XinyiC222/KeyboardX81/Project Files/Kicad/Amelia's Keyboard.kicad_sch

## KiCad design Project Files/Kicad/Amelia's Keyboard.kicad_sch (2026-07-13)

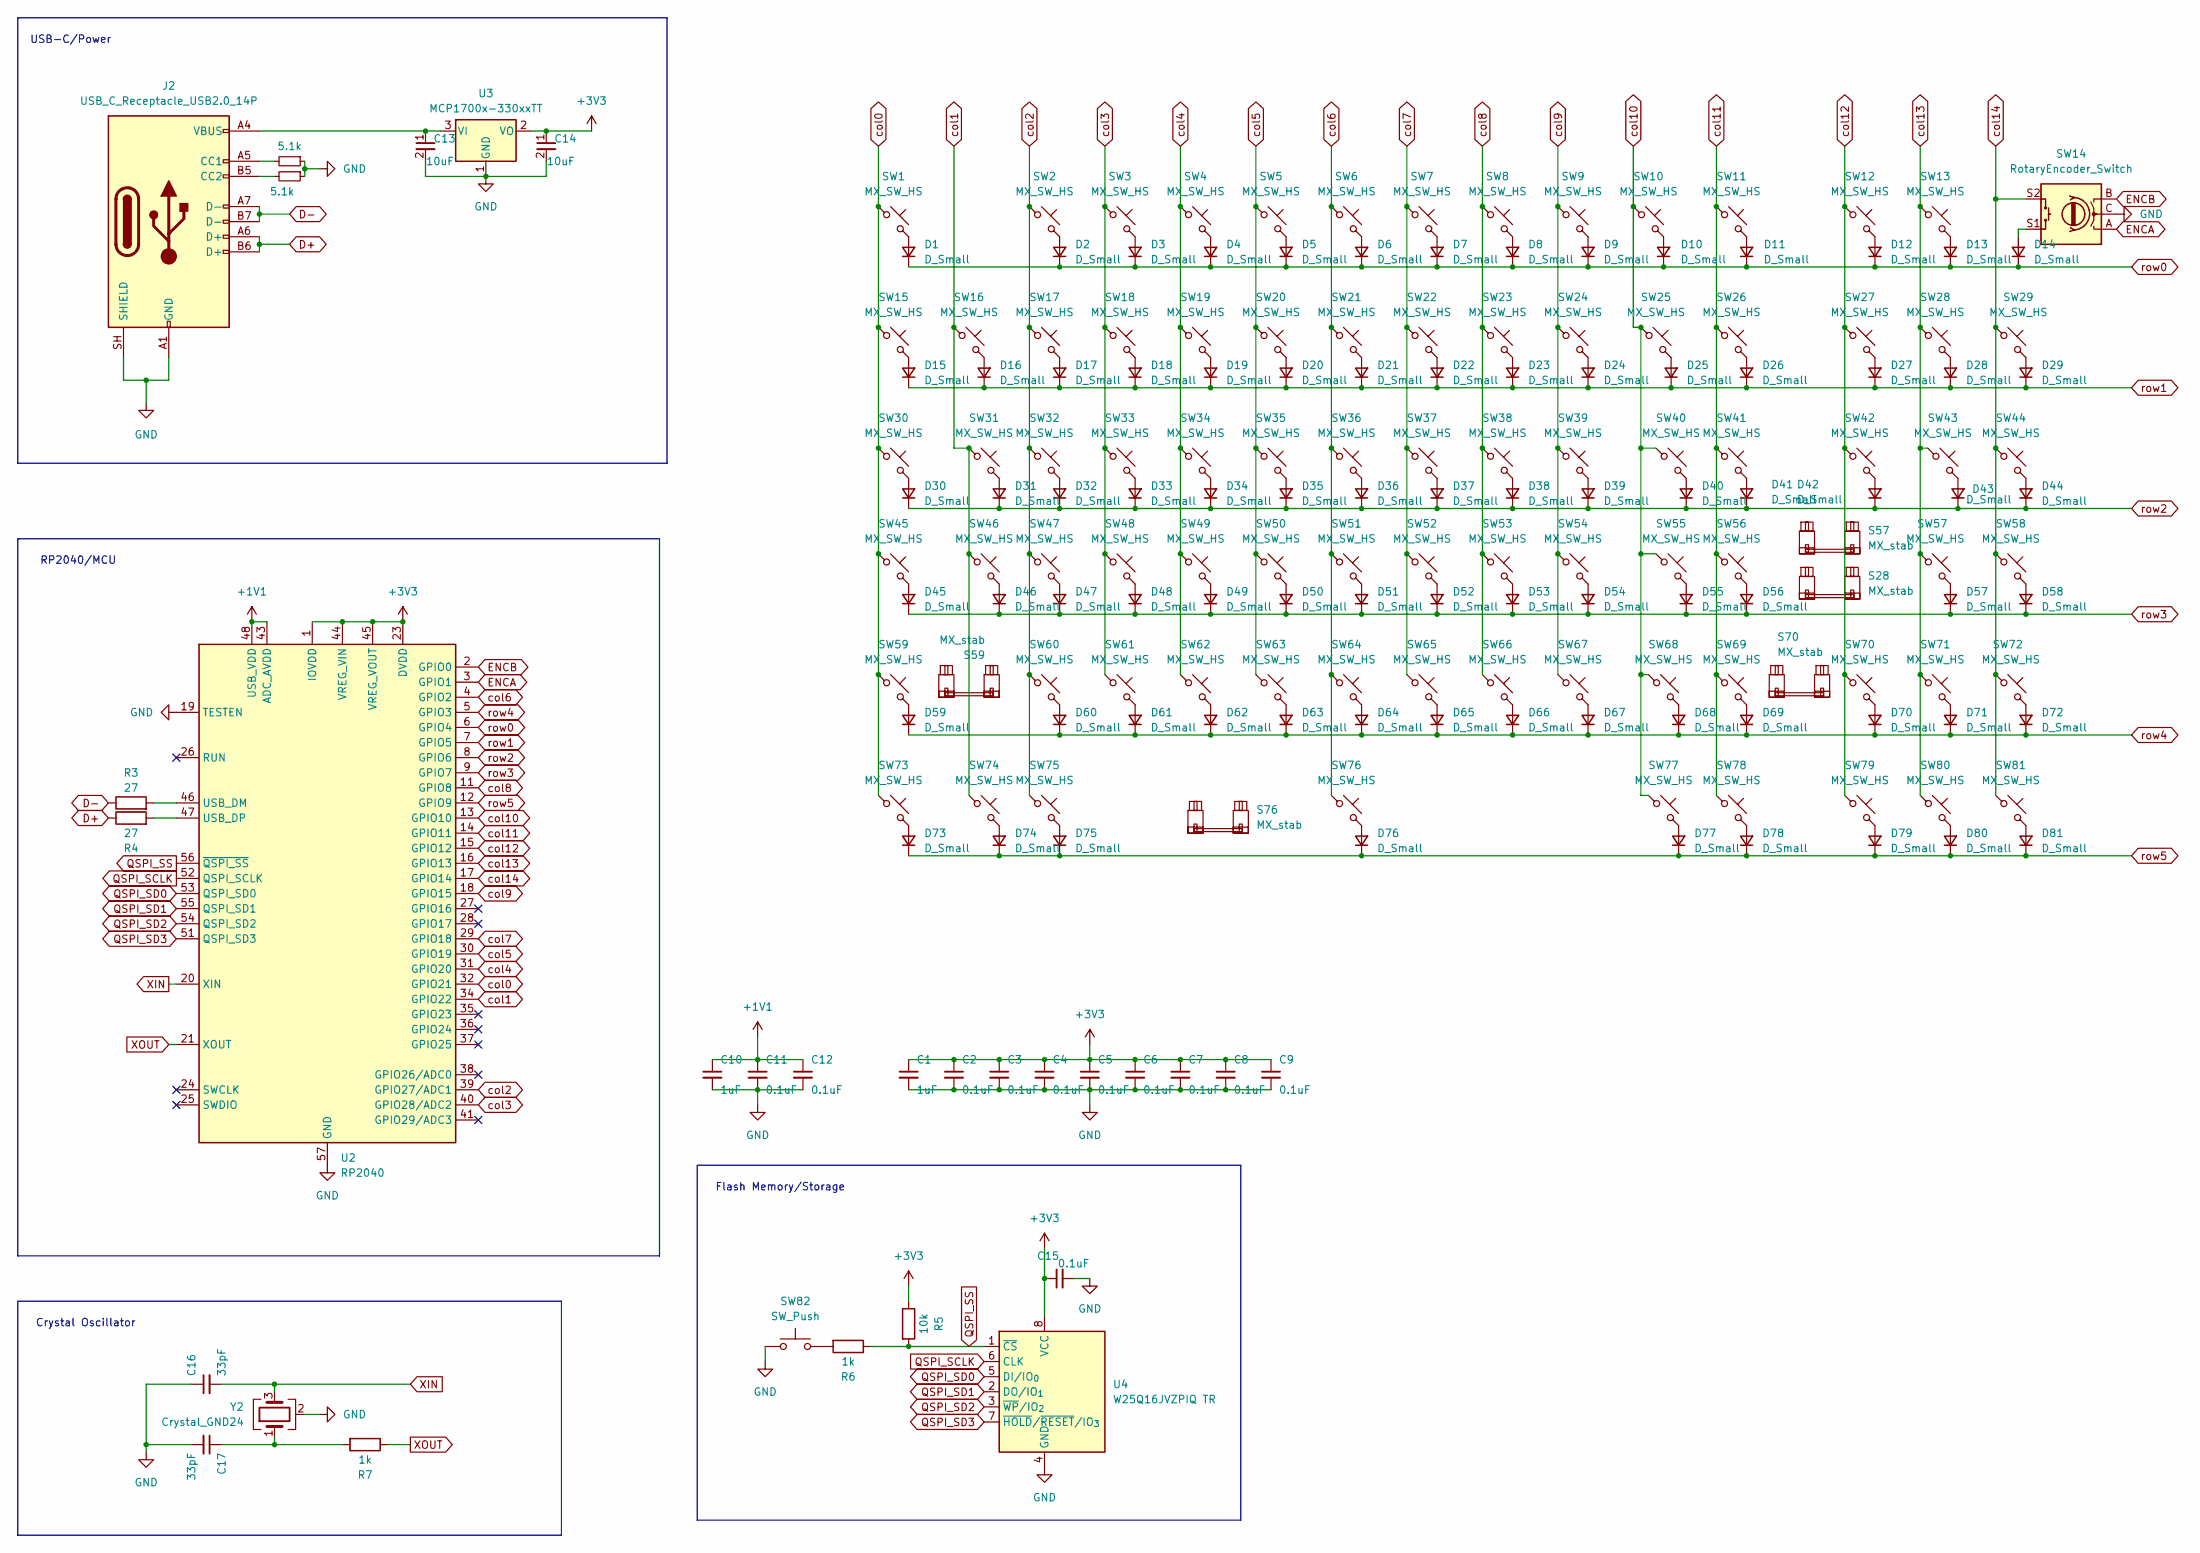
[picture p6: schematic Amelia's Keyboard.kicad_sch]

Parts:
C1, C10: 1uF; C_0402_1005Metric
C2, C3, C4, C5, C6, C7, C8, C9, C11, C12, C15: 0.1uF; C_0402_1005Metric
C13, C14: 10uF; C_0201_0603Metric
C16, C17: 33pF; C_0402_1005Metric
D1, D2, D3, D4, D5, D6, D7, D8, D9, D10, D11, D12, D13, D14, D15, D16, D17, D18, D19, D20, D21, D22, D23, D24, D25, D26, D27, D28, D29, D30, D31, D32, D33, D34, D35, D36, D37, D38, D39, D40, D41, D42, D43, D44, D45, D46, D47, D48, D49, D50, D51, D52, D53, D54, D55, D56, D57, D58, D59, D60, D61, D62, D63, D64, D65, D66, D67, D68, D69, D70, D71, D72, D73, D74, D75, D76, D77, D78, D79, D80, D81: D_Small; D_SOD-123
J2: USB_C_Receptacle_USB2.0_14P; USB_C_Receptacle_HRO_TYPE-C-31-M-12
R1, R2: 5.1k; R_0402_1005Metric
R3, R4: 27; C_0402_1005Metric
R5: 10k; C_0402_1005Metric
R6, R7: 1k; C_0402_1005Metric
S28, S70: MX_stab; STAB_MX_P_2u
S57, S59: MX_stab; STAB_MX_P_2.25u
S76: MX_stab; STAB_MX_P_6.25u
SW1, SW2, SW3, SW4, SW5, SW6, SW7, SW8, SW9, SW10, SW11, SW12, SW13, SW15, SW16, SW17, SW18, SW19, SW20, SW21, SW22, SW23, SW24, SW25, SW26, SW27, SW29, SW31, SW32, SW33, SW34, SW35, SW36, SW37, SW38, SW39, SW40, SW41, SW42, SW44, SW46, SW47, SW48, SW49, SW50, SW51, SW52, SW53, SW54, SW55, SW56, SW58, SW60, SW61, SW62, SW63, SW64, SW65, SW66, SW67, SW68, SW69, SW71, SW72, SW79, SW80, SW81: MX_SW_HS; SW_MX_HS_CPG151101S11_1u
SW14: RotaryEncoder_Switch; Encoder_EC11_MX
SW28, SW57: MX_SW_HS; SW_Hotswap_Kailh_MX_2.00u
SW30, SW43, SW75, SW77: MX_SW_HS; SW_MX_HS_CPG151101S11_1.5u
SW45, SW70: MX_SW_HS; SW_MX_HS_CPG151101S11_1.75u
SW59: MX_SW_HS; SW_Hotswap_Kailh_MX_2.25u
SW73, SW74, SW78: MX_SW_HS; SW_MX_HS_CPG151101S11_1.25u
SW76: MX_SW_HS; SW_Hotswap_Kailh_MX_6.25u
SW82: SW_Push; SW_Push_SPST_NO_Alps_SKRK
U2: RP2040; QFN-56-1EP_7x7mm_P0.4mm_EP3.2x3.2mm
U3: MCP1700x-330xxTT; SOT-23
U4: W25Q16JVZPIQ TR; Winbond_USON-8-1EP_3x2mm_P0.5mm_EP0.2x1.6mm
Y2: Crystal_GND24; Crystal_SMD_3225-4Pin_3.2x2.5mm

Connections:
+1V1: C10.1, C11.1, C12.1, U2.43 (ADC_AVDD), U2.48 (USB_VDD)
+3V3: C1.1, C2.1, C3.1, C4.1, C5.1, C6.1, C7.1, C8.1, C9.1, C14.1, C15.1, R5.1, U2.1 (IOVDD), U2.10 (IOVDD), U2.22 (IOVDD), U2.23 (DVDD), U2.33 (IOVDD), U2.42 (IOVDD), U2.44 (VREG_VIN), U2.45 (VREG_VOUT), U2.49 (IOVDD), U2.50 (DVDD), U3.2 (VO), U4.8 (VCC)
D+: J2.A6 (D+), J2.B6 (D+), R4.1
D-: J2.A7 (D-), J2.B7 (D-), R3.1
ENCA: SW14.A, U2.3 (GPIO1)
ENCB: SW14.B, U2.2 (GPIO0)
GND: C1.2, C2.2, C3.2, C4.2, C5.2, C6.2, C7.2, C8.2, C9.2, C10.2, C11.2, C12.2, C13.2, C14.2, C15.2, C16.1, C17.2, J2.A1 (GND), J2.A12 (GND), J2.B1 (GND), J2.B12 (GND), J2.SH (SHIELD), R1.1, R2.1, SW14.C, SW82.1, U2.19 (TESTEN), U2.57 (GND), U3.1 (GND), U4.4 (GND), Y2.2 (G), Y2.4 (G)
unnamed: C13.1, J2.A4 (VBUS), J2.A9 (VBUS), J2.B4 (VBUS), J2.B9 (VBUS), U3.3 (VI)
unnamed: C17.1, R7.2, Y2.1
unnamed: D1.2 (A), SW1.2
unnamed: D2.2 (A), SW2.2
unnamed: D3.2 (A), SW3.2
unnamed: D4.2 (A), SW4.2
unnamed: D5.2 (A), SW5.2
unnamed: D6.2 (A), SW6.2
unnamed: D7.2 (A), SW7.2
unnamed: D8.2 (A), SW8.2
unnamed: D9.2 (A), SW9.2
unnamed: D10.2 (A), SW10.2
unnamed: D11.2 (A), SW11.2
unnamed: D12.2 (A), SW12.2
unnamed: D13.2 (A), SW13.2
unnamed: D14.2 (A), SW14.S1
unnamed: D15.2 (A), SW15.2
unnamed: D16.2 (A), SW16.2
unnamed: D17.2 (A), SW17.2
unnamed: D18.2 (A), SW18.2
unnamed: D19.2 (A), SW19.2
unnamed: D20.2 (A), SW20.2
unnamed: D21.2 (A), SW21.2
unnamed: D22.2 (A), SW22.2
unnamed: D23.2 (A), SW23.2
unnamed: D24.2 (A), SW24.2
unnamed: D25.2 (A), SW25.2
unnamed: D26.2 (A), SW26.2
unnamed: D27.2 (A), SW27.2
unnamed: D28.2 (A), SW28.2
unnamed: D29.2 (A), SW29.2
unnamed: D30.2 (A), SW30.2
unnamed: D31.2 (A), SW31.2
unnamed: D32.2 (A), SW32.2
unnamed: D33.2 (A), SW33.2
unnamed: D34.2 (A), SW34.2
unnamed: D35.2 (A), SW35.2
unnamed: D36.2 (A), SW36.2
unnamed: D37.2 (A), SW37.2
unnamed: D38.2 (A), SW38.2
unnamed: D39.2 (A), SW39.2
unnamed: D40.2 (A), SW40.2
unnamed: D41.2 (A), SW41.2
unnamed: D42.2 (A), SW42.2
unnamed: D43.2 (A), SW43.2
unnamed: D44.2 (A), SW44.2
unnamed: D45.2 (A), SW45.2
unnamed: D46.2 (A), SW46.2
unnamed: D47.2 (A), SW47.2
unnamed: D48.2 (A), SW48.2
unnamed: D49.2 (A), SW49.2
unnamed: D50.2 (A), SW50.2
unnamed: D51.2 (A), SW51.2
unnamed: D52.2 (A), SW52.2
unnamed: D53.2 (A), SW53.2
unnamed: D54.2 (A), SW54.2
unnamed: D55.2 (A), SW55.2
unnamed: D56.2 (A), SW56.2
unnamed: D57.2 (A), SW57.2
unnamed: D58.2 (A), SW58.2
unnamed: D59.2 (A), SW59.2
unnamed: D60.2 (A), SW60.2
unnamed: D61.2 (A), SW61.2
unnamed: D62.2 (A), SW62.2
unnamed: D63.2 (A), SW63.2
unnamed: D64.2 (A), SW64.2
unnamed: D65.2 (A), SW65.2
unnamed: D66.2 (A), SW66.2
unnamed: D67.2 (A), SW67.2
unnamed: D68.2 (A), SW68.2
unnamed: D69.2 (A), SW69.2
unnamed: D70.2 (A), SW70.2
unnamed: D71.2 (A), SW71.2
unnamed: D72.2 (A), SW72.2
unnamed: D73.2 (A), SW73.2
unnamed: D74.2 (A), SW74.2
unnamed: D75.2 (A), SW75.2
unnamed: D76.2 (A), SW76.2
unnamed: D77.2 (A), SW77.2
unnamed: D78.2 (A), SW78.2
unnamed: D79.2 (A), SW79.2
unnamed: D80.2 (A), SW80.2
unnamed: D81.2 (A), SW81.2
unnamed: J2.A5 (CC1), R1.2
unnamed: J2.B5 (CC2), R2.2
unnamed: R3.2, U2.46 (USB_DM)
unnamed: R4.2, U2.47 (USB_DP)
unnamed: R6.2, SW82.2
QSPI_SCLK: U2.52 (QSPI_SCLK), U4.6 (CLK)
QSPI_SD0: U2.53 (QSPI_SD0), U4.5 (DI/IO_{0})
QSPI_SD1: U2.55 (QSPI_SD1), U4.2 (DO/IO_{1})
QSPI_SD2: U2.54 (QSPI_SD2), U4.3 (~WP/IO_{2})
QSPI_SD3: U2.51 (QSPI_SD3), U4.7 (~HOLD/~RESET/IO_{3})
QSPI_SS: R5.2, R6.1, U2.56 (~QSPI_SS), U4.1 (~CS)
XIN: C16.2, U2.20 (XIN), Y2.3
XOUT: R7.1, U2.21 (XOUT)
col0: SW1.1, SW15.1, SW30.1, SW45.1, SW59.1, SW73.1, U2.32 (GPIO21)
col1: SW16.1, SW31.1, SW46.1, SW74.1, U2.34 (GPIO22)
col2: SW2.1, SW17.1, SW32.1, SW47.1, SW60.1, SW75.1, U2.39 (GPIO27/ADC1)
col3: SW3.1, SW18.1, SW33.1, SW48.1, SW61.1, U2.40 (GPIO28/ADC2)
col4: SW4.1, SW19.1, SW34.1, SW49.1, SW62.1, U2.31 (GPIO20)
col5: SW5.1, SW20.1, SW35.1, SW50.1, SW63.1, U2.30 (GPIO19)
col6: SW6.1, SW21.1, SW36.1, SW51.1, SW64.1, SW76.1, U2.4 (GPIO2)
col7: SW7.1, SW22.1, SW37.1, SW52.1, SW65.1, U2.29 (GPIO18)
col8: SW8.1, SW23.1, SW38.1, SW53.1, SW66.1, U2.11 (GPIO8)
col9: SW9.1, SW24.1, SW39.1, SW54.1, SW67.1, U2.18 (GPIO15)
col10: SW10.1, SW25.1, SW40.1, SW55.1, SW68.1, SW77.1, U2.13 (GPIO10)
col11: SW11.1, SW26.1, SW41.1, SW56.1, SW69.1, SW78.1, U2.14 (GPIO11)
col12: SW12.1, SW27.1, SW42.1, SW70.1, SW79.1, U2.15 (GPIO12)
col13: SW13.1, SW28.1, SW43.1, SW57.1, SW71.1, SW80.1, U2.16 (GPIO13)
col14: SW14.S2, SW29.1, SW44.1, SW58.1, SW72.1, SW81.1, U2.17 (GPIO14)
row0: D1.1 (K), D2.1 (K), D3.1 (K), D4.1 (K), D5.1 (K), D6.1 (K), D7.1 (K), D8.1 (K), D9.1 (K), D10.1 (K), D11.1 (K), D12.1 (K), D13.1 (K), D14.1 (K), U2.6 (GPIO4)
row1: D15.1 (K), D16.1 (K), D17.1 (K), D18.1 (K), D19.1 (K), D20.1 (K), D21.1 (K), D22.1 (K), D23.1 (K), D24.1 (K), D25.1 (K), D26.1 (K), D27.1 (K), D28.1 (K), D29.1 (K), U2.7 (GPIO5)
row2: D30.1 (K), D31.1 (K), D32.1 (K), D33.1 (K), D34.1 (K), D35.1 (K), D36.1 (K), D37.1 (K), D38.1 (K), D39.1 (K), D40.1 (K), D41.1 (K), D42.1 (K), D43.1 (K), D44.1 (K), U2.8 (GPIO6)
row3: D45.1 (K), D46.1 (K), D47.1 (K), D48.1 (K), D49.1 (K), D50.1 (K), D51.1 (K), D52.1 (K), D53.1 (K), D54.1 (K), D55.1 (K), D56.1 (K), D57.1 (K), D58.1 (K), U2.9 (GPIO7)
row4: D59.1 (K), D60.1 (K), D61.1 (K), D62.1 (K), D63.1 (K), D64.1 (K), D65.1 (K), D66.1 (K), D67.1 (K), D68.1 (K), D69.1 (K), D70.1 (K), D71.1 (K), D72.1 (K), U2.5 (GPIO3)
row5: D73.1 (K), D74.1 (K), D75.1 (K), D76.1 (K), D77.1 (K), D78.1 (K), D79.1 (K), D80.1 (K), D81.1 (K), U2.12 (GPIO9)

Notes on the sheet:
Flash Memory/Storage
Crystal Oscillator
USB-C/Power
RP2040/MCU
